PushpalDas/Learning-Aid-for-Children-with-Motor-Neuron-Defect-/CERTIFICATE-IUCEE/Pushpal Das POPBL Certificate.pptx.pdf

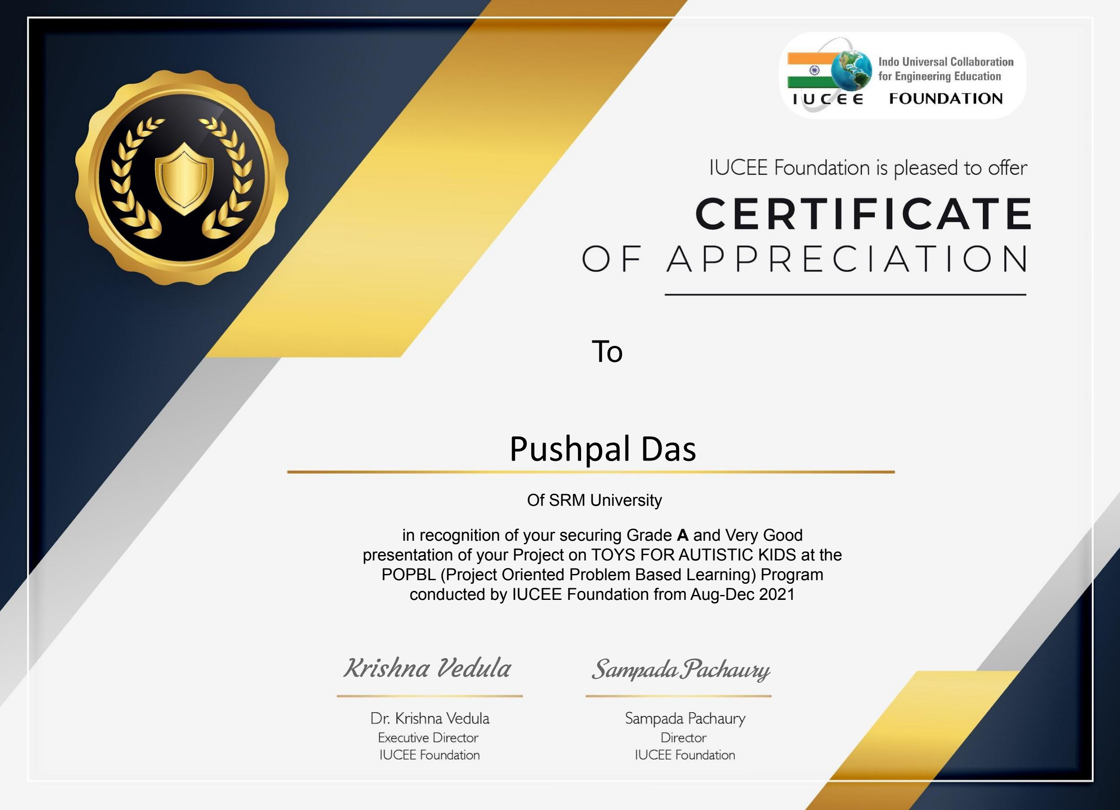
[picture p69: page 1]

# Pushpal Das

Of SRM University

in recognition of your securing Grade A and Very Good presentation of your Project on TOYS FOR AUTISTIC KIDS at the POPBL (Project Oriented Problem Based Learning) Program conducted by IUCEE Foundation from Aug-Dec 2021

To

# Krishna Vedula Sampada Pachaury
