PushpalDas/Learning-Aid-for-Children-with-Motor-Neuron-Defect-/IGES FILES/PHOTO-2022-01-13-23-20-00(2).jpg

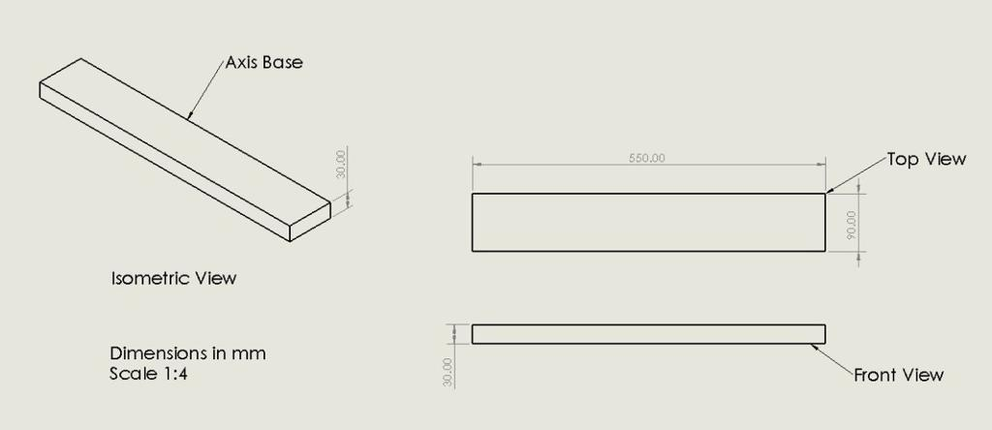
IGES FILES/PHOTO-2022-01-13-23-20-00(2).jpg
