PushpalDas/Learning-Aid-for-Children-with-Motor-Neuron-Defect-/IGES FILES/PHOTO-2022-01-13-23-20-01(14).jpg

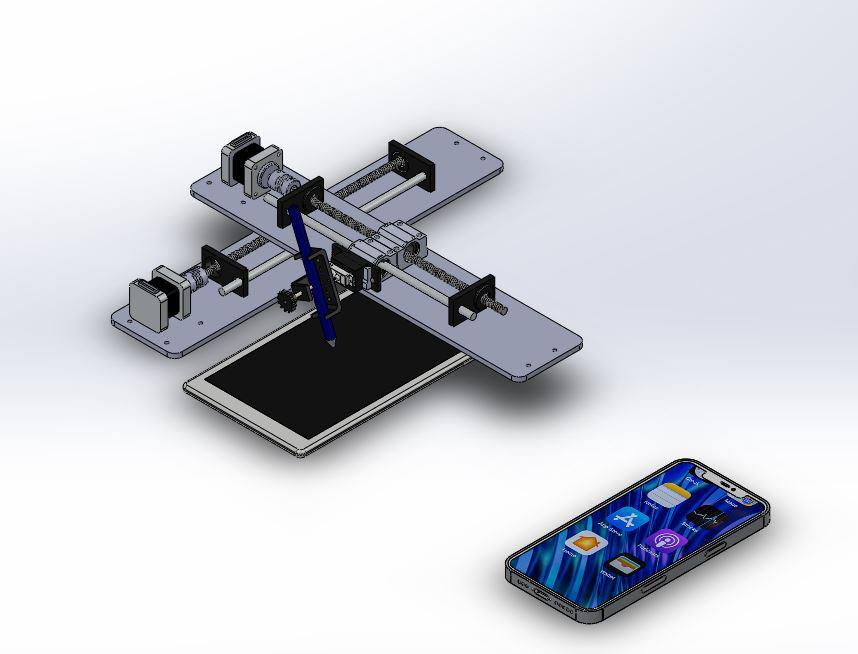
IGES FILES/PHOTO-2022-01-13-23-20-01(14).jpg
