PushpalDas/Learning-Aid-for-Children-with-Motor-Neuron-Defect-/Thinktech2k21/CERTIFICATE participation.png

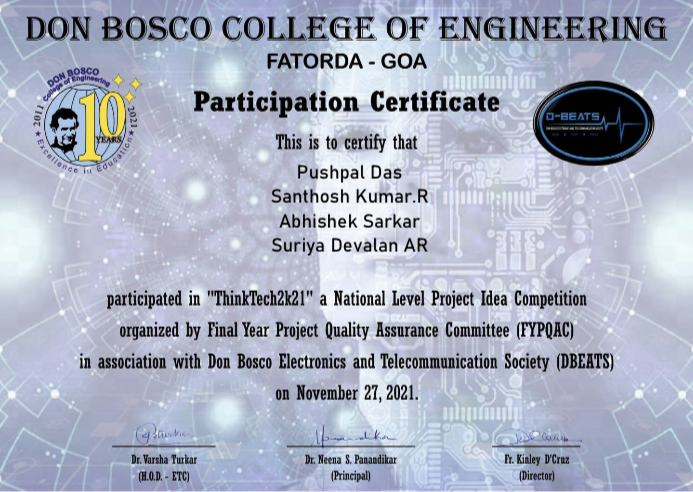
Thinktech2k21/CERTIFICATE participation.png
