PushpalDas/Learning-Aid-for-Children-with-Motor-Neuron-Defect-/Thinktech2k21/Final round.png

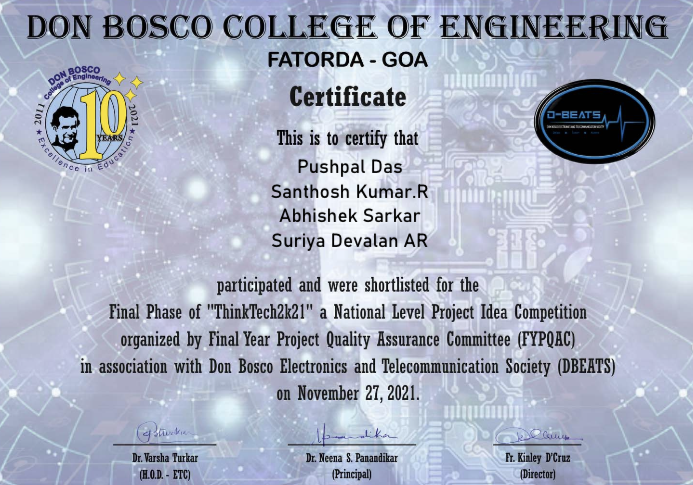
Thinktech2k21/Final round.png
